Roland-Scholz/FABIAN/src/mc68681.asm

;--------------------------------------------------------------------------------
; equates for MC68681 DUART
;
; see ./doc/scc68681.pdf
;--------------------------------------------------------------------------------
MODEA		equ	0
STATA		equ	1
CLOCKA		equ	1
COMMA		equ	2
RECA		equ	3
TRANSA		equ	3
IPCHANGE	equ	4
AUXCTRL		equ	4
ISR		equ	5
IMR		equ	5
CNTMSB		equ	6
CNTLSB		equ	7
MODEB		equ	8
STATB		equ	9
CLOCKB		equ	9
COMMB		equ	10
RECB		equ	11
TRANSB		equ	11
IVR		equ	12
INPORT		equ	13
OPCTRL		equ	13
STRTCNT		equ	14
OPSET		equ	14
STOPCNT		equ	15
OPRES		equ	15
